RooK-Computer/RooK-Mk3/STLs/LegoInspiredCase_by_Konnexus_Mk1/CartridgeMk2-STLs/CartridgeMk2-TopPanel.stl

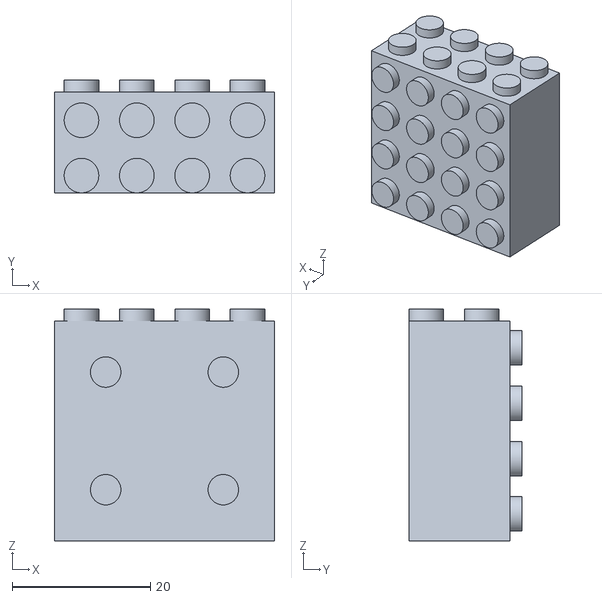
[picture p16: CAD file, 2025-09-18]
STLs/LegoInspiredCase_by_Konnexus_Mk1/CartridgeMk2-STLs/CartridgeMk2-TopPanel.stl
31.8 x 16.3 x 33.5
