RooK-Computer/RooK-Mk3/STLs/LegoInspiredCase_by_Konnexus_Mk1/CartridgeMk2-STLs/CartridgeMk2-FrontSide.stl

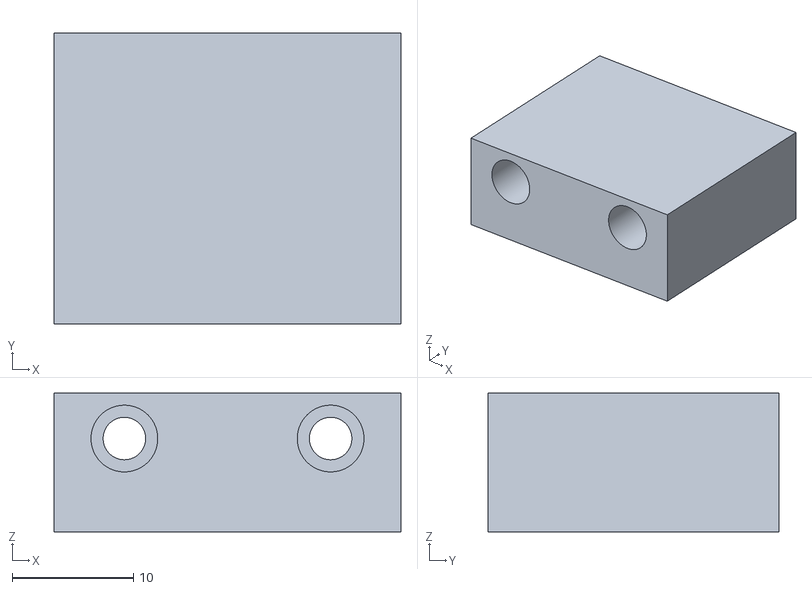
[picture p17: CAD file, 2025-09-12]
STLs/LegoInspiredCase_by_Konnexus_Mk1/CartridgeMk2-STLs/CartridgeMk2-FrontSide.stl
28.6 x 24.0 x 11.5
