RooK-Computer/RooK-Mk3/STLs/LegoInspiredCase_by_Konnexus_Mk1/Case-STLs/LegoCase_Konnexus_Mk1-Quit Button fat Border.stl

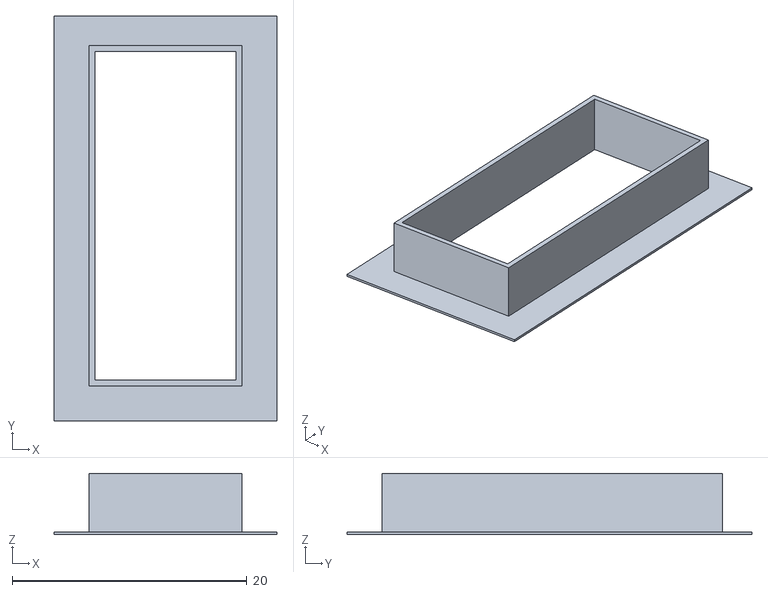
[picture p18: CAD file, 2025-09-19]
STLs/LegoInspiredCase_by_Konnexus_Mk1/Case-STLs/LegoCase_Konnexus_Mk1-Quit Button fat Border.stl
19.0 x 34.5 x 5.20
