RooK-Computer/RooK-Mk3/STLs/LegoInspiredCase_by_Konnexus_Mk1/CartridgeMk2-STLs/CartridgeMk2-Housing.stl

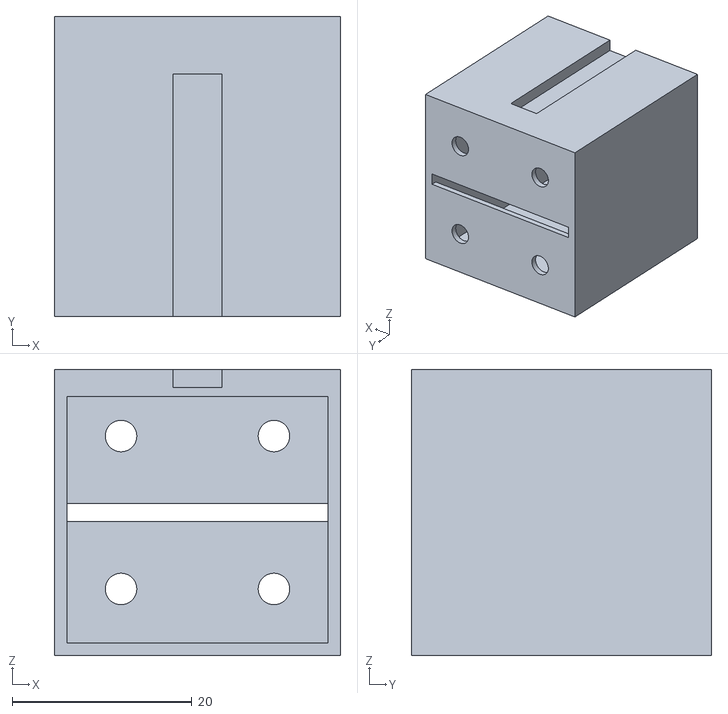
[picture p19: CAD file, 2025-09-12]
STLs/LegoInspiredCase_by_Konnexus_Mk1/CartridgeMk2-STLs/CartridgeMk2-Housing.stl
31.8 x 33.4 x 31.8
