RooK-Computer/RooK-Mk3/STLs/LegoInspiredCase_by_Konnexus_Mk1/Case-STLs/LegoCase_Konnexus_Mk1-Quit Button fat revised.stl

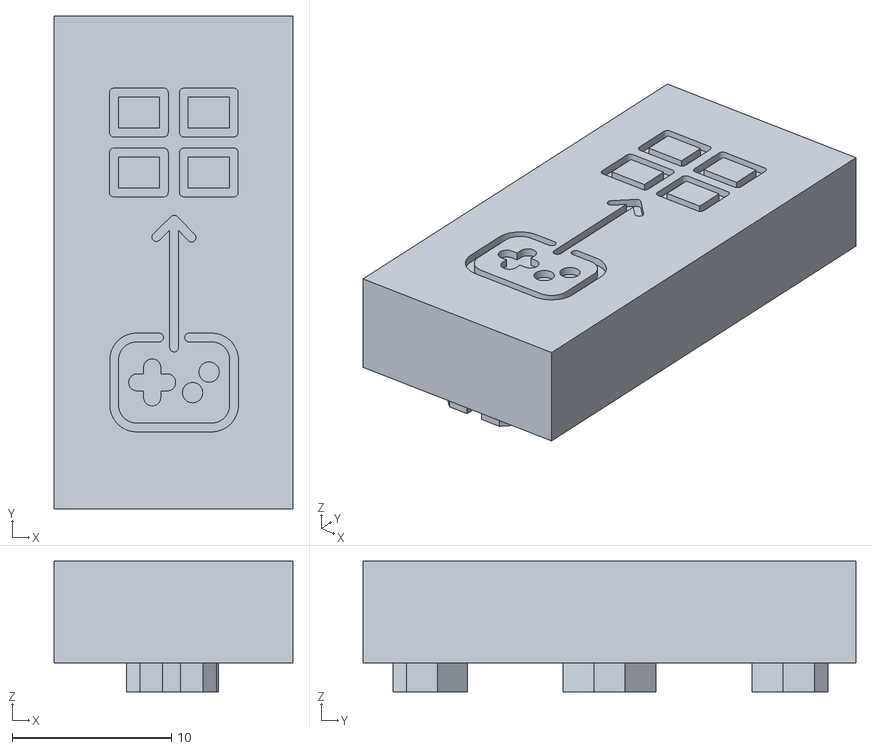
[picture p20: CAD file, 2025-09-19]
STLs/LegoInspiredCase_by_Konnexus_Mk1/Case-STLs/LegoCase_Konnexus_Mk1-Quit Button fat revised.stl
15.0 x 31.0 x 8.21
