RooK-Computer/RooK-Mk3/STLs/LegoInspiredCase_by_Konnexus_Mk1/Case-STLs/LegoCase_Konnexus_Mk1-Shutdown Button Print.stl

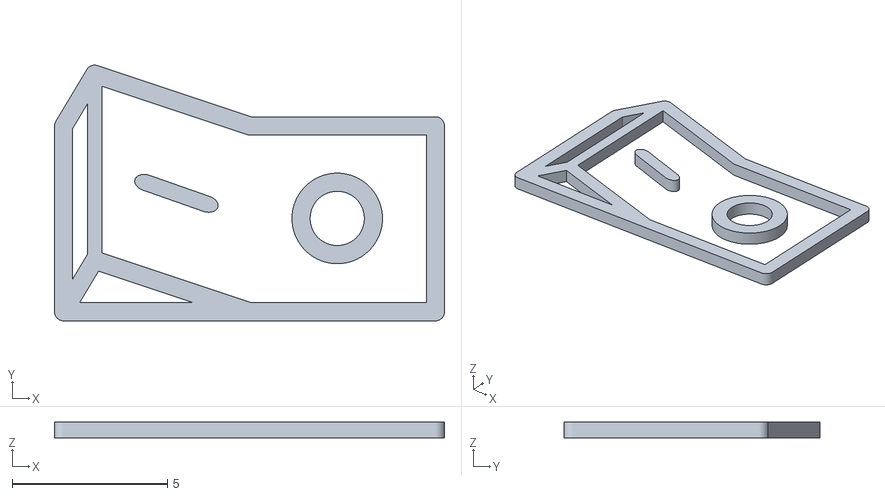
[picture p21: CAD file, 2025-09-12]
STLs/LegoInspiredCase_by_Konnexus_Mk1/Case-STLs/LegoCase_Konnexus_Mk1-Shutdown Button Print.stl
12.6 x 8.24 x 0.5
