RooK-Computer/RooK-Mk3/STLs/LegoInspiredCase_by_Konnexus_Mk1/Case-STLs/LegoCase_Konnexus_Mk1-CaseBase.stl

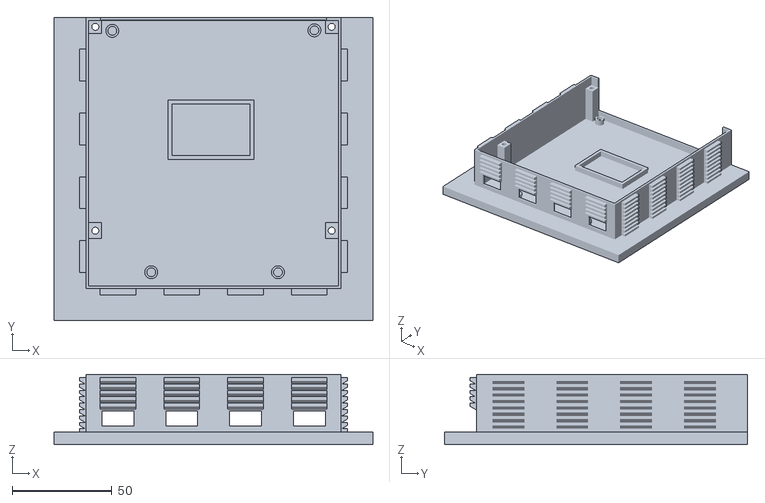
[picture p22: CAD file, 2025-09-12]
STLs/LegoInspiredCase_by_Konnexus_Mk1/Case-STLs/LegoCase_Konnexus_Mk1-CaseBase.stl
159.8 x 151.8 x 35.2
