RooK-Computer/RooK-Mk3/STLs/LegoInspiredCase_by_Konnexus_Mk1/Case-STLs/LegoCase_Konnexus_Mk1-cover embossed.stl

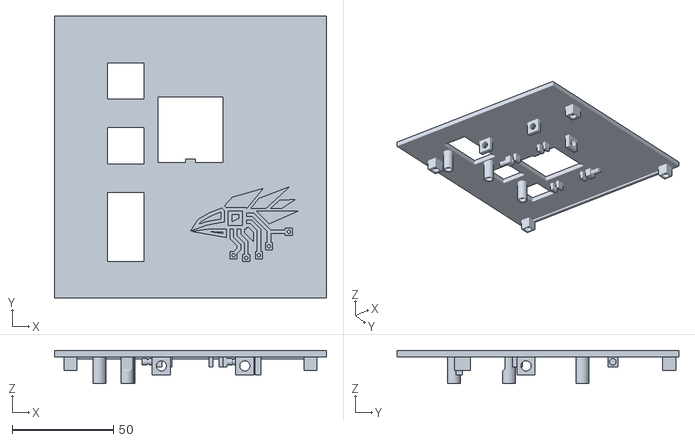
[picture p23: CAD file, 2025-09-12]
STLs/LegoInspiredCase_by_Konnexus_Mk1/Case-STLs/LegoCase_Konnexus_Mk1-cover embossed.stl
134.2 x 139.0 x 16.5
