RooK-Computer/RooK-Mk3/STLs/LegoInspiredCase_by_Konnexus_Mk1/Case-STLs/LegoCase_Konnexus_Mk1-KeySwitchSolderingHolder.stl

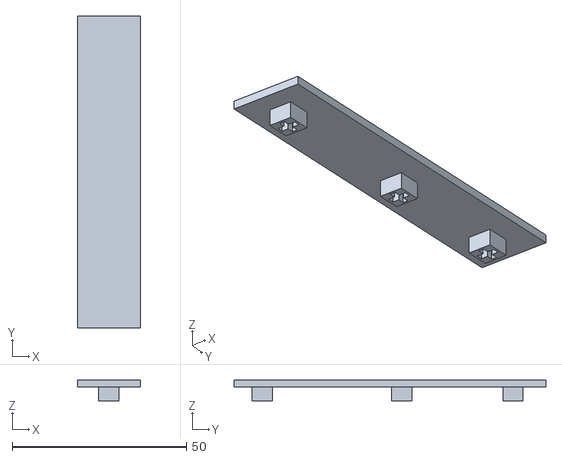
[picture p24: CAD file, 2025-09-12]
STLs/LegoInspiredCase_by_Konnexus_Mk1/Case-STLs/LegoCase_Konnexus_Mk1-KeySwitchSolderingHolder.stl
18.1 x 89.6 x 6.00
