RooK-Computer/RooK-Mk3/STLs/LegoInspiredCase_by_Konnexus_Mk1/Case-STLs/LegoCase_Konnexus_Mk1-Reset Button fat print.stl

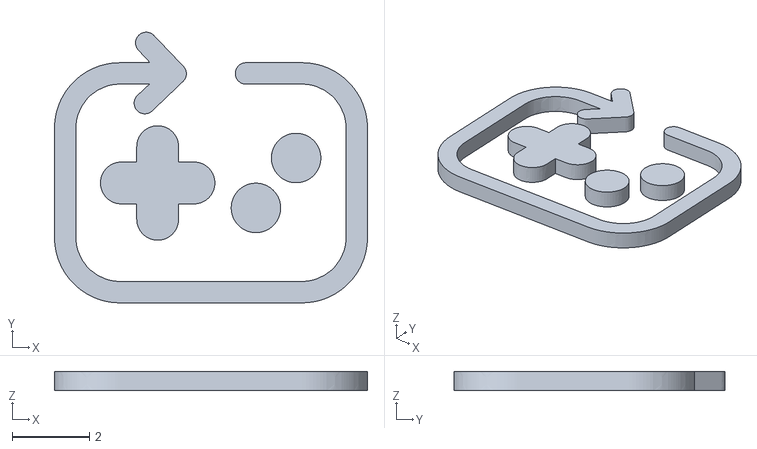
[picture p25: CAD file, 2025-09-12]
STLs/LegoInspiredCase_by_Konnexus_Mk1/Case-STLs/LegoCase_Konnexus_Mk1-Reset Button fat print.stl
8.09 x 7.00 x 0.5
