RooK-Computer/RooK-Mk3/PCBs/CartridgeReader/CartridgeMk3ReaderMk6/CartridgeMk3ReaderMk6.pdf

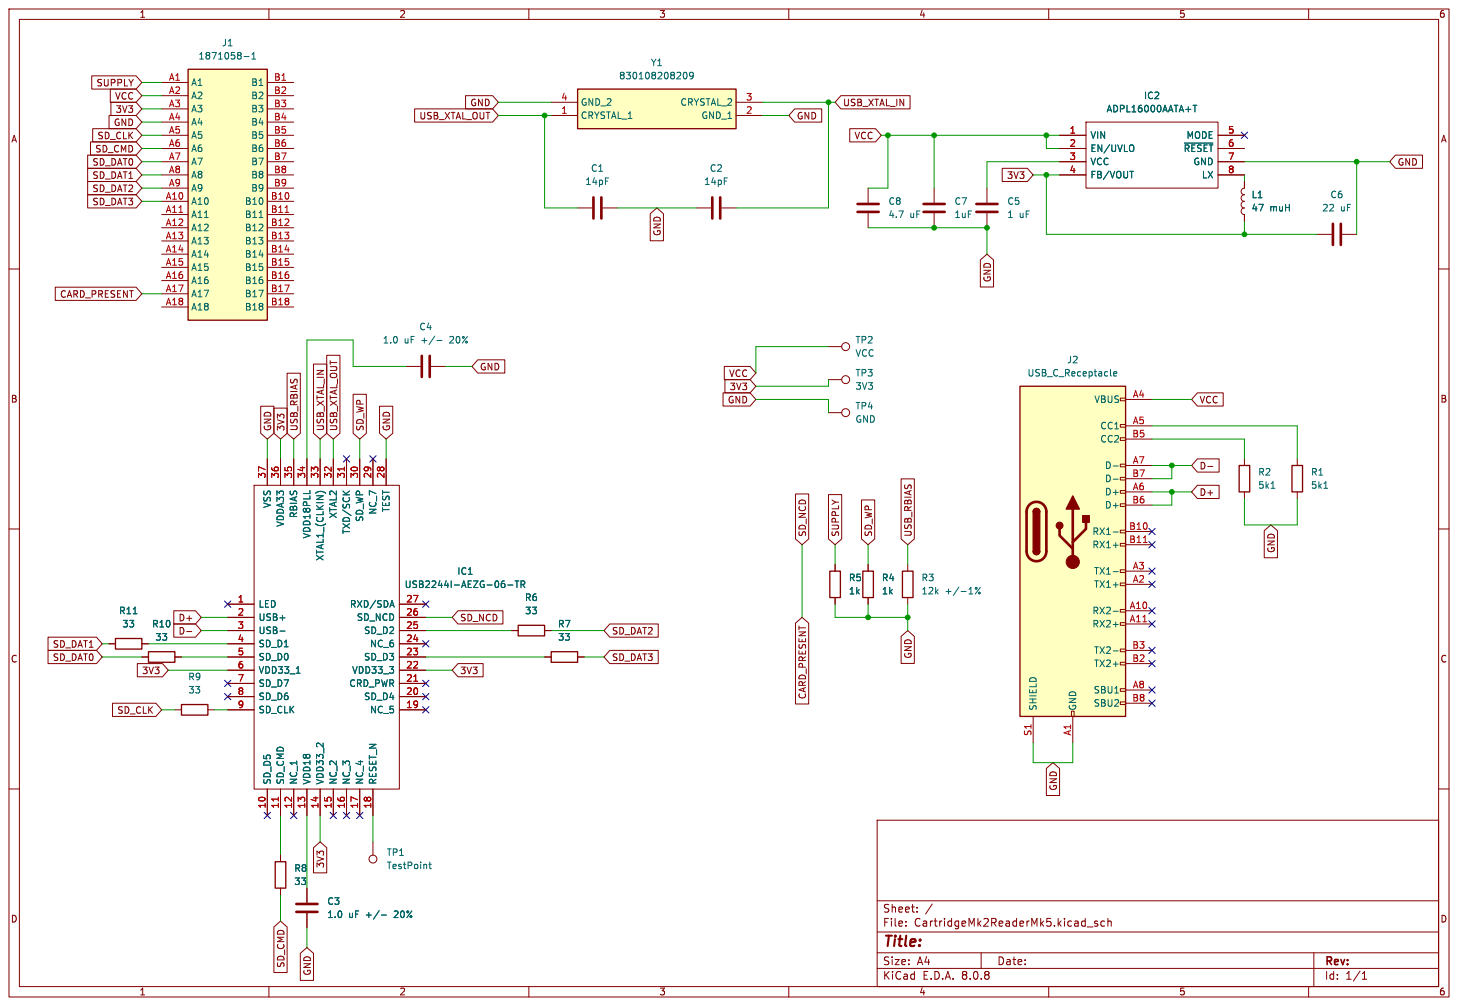
[picture p33: page 1]

Id: 1/1 Title: File: CartridgeMk2ReaderMk5.kicad_sch Sheet: /R3
