RooK-Computer/RooK-Mk3/PCBs/CM4-Files/CM4IO-KiCAD/CM4IOv5.kicad_sch

## KiCad design PCBs/CM4-Files/CM4IO-KiCAD/CM4IOv5.kicad_sch (2025-09-12)

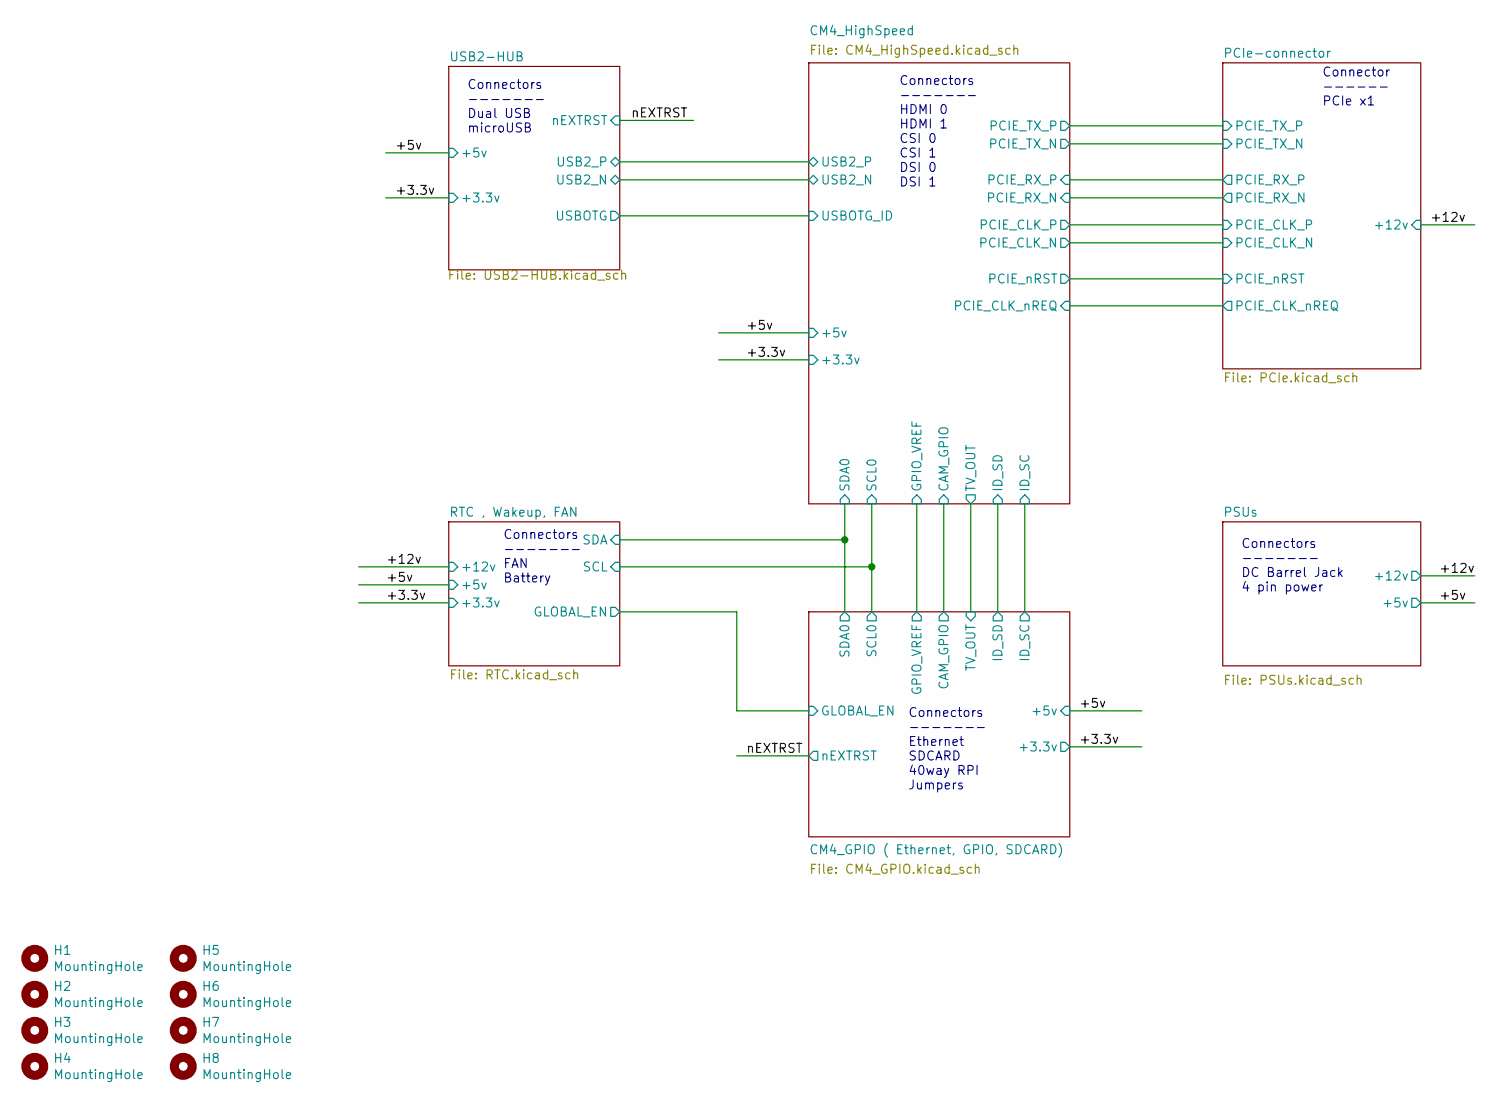
[picture p46: schematic CM4IOv5.kicad_sch]

Parts:
H1, H2, H3, H4, H5, H6, H7, H8: MountingHole; MountingHole_2.7mm_M2.5; Part Description M2.5 mounting hole

Notes on the sheet:
Connectors ------- FAN Battery
Connector ------ PCIe x1
Connectors ------- DC Barrel Jack 4 pin power
Connectors ------- Dual USB microUSB
Connectors ------- Ethernet SDCARD 40way RPI Jumpers
Connectors ------- HDMI 0 HDMI 1 CSI 0 CSI 1 DSI 0 DSI 1
