RooK-Computer/RooK-Mk3/PCBs/CM4-Files/CM4IO-KiCAD/CM4_GPIO.kicad_sch

## KiCad design PCBs/CM4-Files/CM4IO-KiCAD/CM4_GPIO.kicad_sch (2025-09-12)

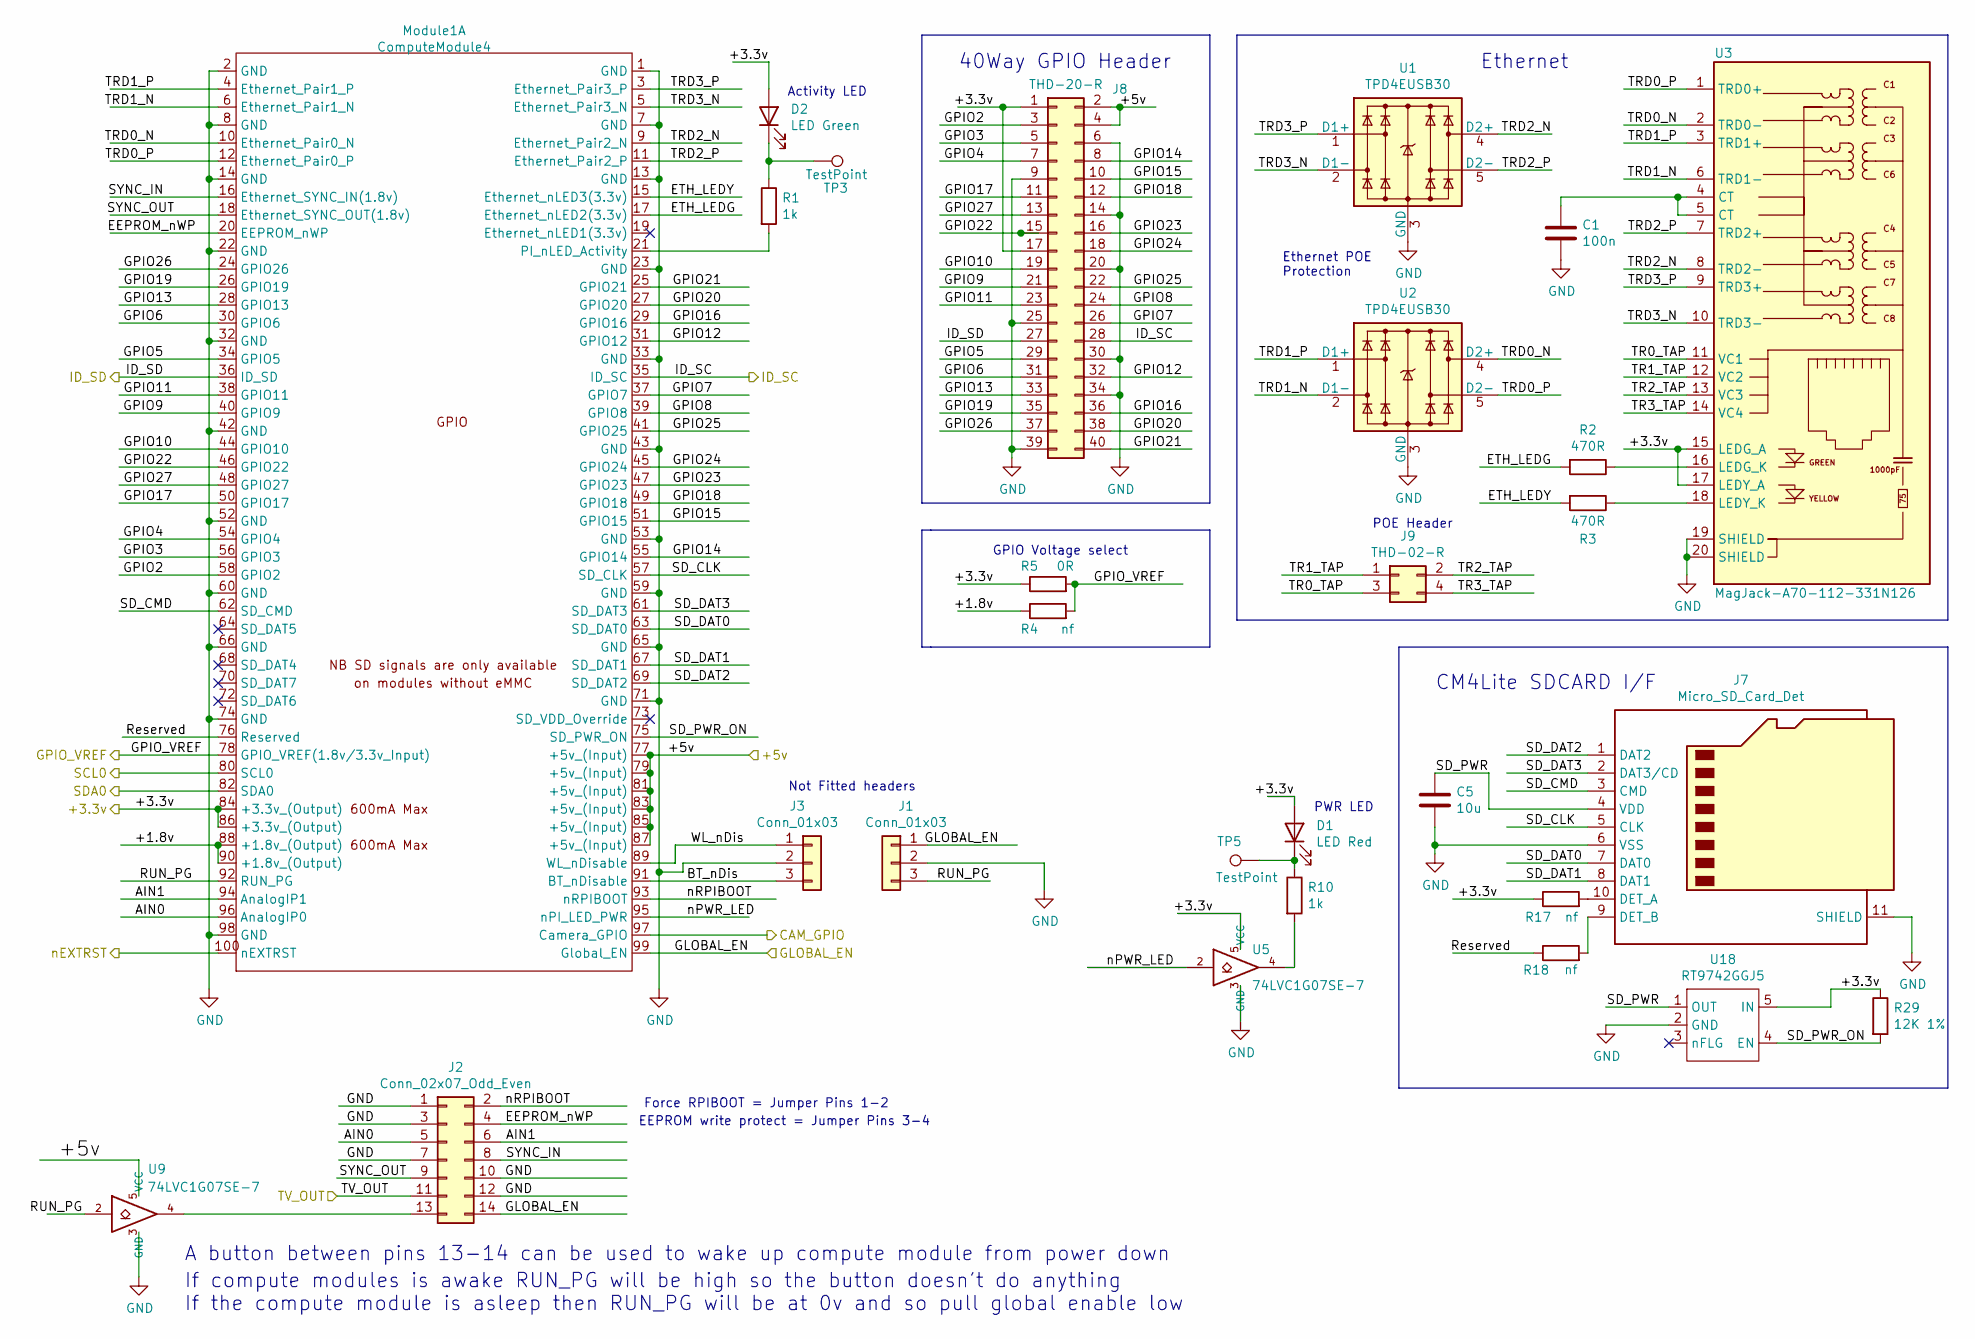
[picture p47: schematic CM4_GPIO.kicad_sch]

Parts:
C1: 100n; C_0402_1005Metric; Part Description 0.1uF 10% 16V Ceramic Capacitor X7R 040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
C5: 10u; C_0805_2012Metric; Part Description 10uF 10% 10V Ceramic Capacitor X7R 0805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
D1: LED Red; LED_0603_1608Metric; Part Description Red 620nm LED Indication - Discrete 2.2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
D2: LED Green; LED_0603_1608Metric; Part Description Green 572nm LED Indication - Discrete 2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
J1, J3: Conn_01x03; PinHeader_1x03_P2.54mm_Vertical; Part Description 3pin 0.1" connector
J2: Conn_02x07_Odd_Even; PinHeader_2x07_P2.54mm_Vertical; Part Description PinHeader_2x07_P2.54mm_Vertical
J7: Micro_SD_Card_Det; SDCARD_MOLEX_503398-1892; Part Description 9 (8 + 1) Position Card Connector micro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
J8: THD-20-R; PinHeader_2x20_P2.54mm_Vertical; Part Description PinHeader_2x20_P2.54mm_Vertical
J9: THD-02-R; PinHeader_2x02_P2.54mm_Vertical; Part Description PinHeader_2x02_P2.54mm_Vertical
Module1: ComputeModule4; Raspberry-Pi-4-Compute-Module; Part Description 100 Position Connector Receptacle, Cent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
R1, R10: 1k; R_0402_1005Metric; Part Description Resistor 1K M1005 1% 63mW
R2, R3: 470R; R_0402_1005Metric; Part Description Resistor 470R M1005 1% 63mW
R4: nf; R_0805_2012Metric_Pad1.15x1.40mm_HandSolder
R5: 0R; R_0805_2012Metric_Pad1.15x1.40mm_HandSolder; Part Description Resistor 0R M2012 5%
R17, R18: nf; R_0402_1005Metric; Part Description Resistor 1K M1005 1% 63mW
R29: 12K 1%; R_0402_1005Metric; Part Description Resistor 12K M1005 1% 63mW
TP3, TP5: TestPoint; TestPoint_Pad_2.0x2.0mm
U1, U2: TPD4EUSB30; USON-10_2.5x1.0mm_P0.5mm; Part Description Quad TVS diode for high speed signals (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
U3: MagJack-A70-112-331N126; TRJG0926HENL; Part Description Gigabit Ethernet Magjack
U5, U9: 74LVC1G07SE-7; SOT-353_SC-70-5; Part Description Buffer, Non-Inverting 1 Element 1 Bit p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
U18: RT9742GGJ5; SOT-23-5; Part Description Power Switch/Driver 1:1 N-Channel 1A TS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

Connections:
+1.8v: Module1.88 (+1.8v_(Output)), Module1.90 (+1.8v_(Output)), R4.1
+3.3v: D1.2 (A), D2.2 (A), J8.1, J8.17, Module1.84 (+3.3v_(Output)), Module1.86 (+3.3v_(Output)), R5.1, R17.1, R29.1, U3.15 (LEDG_A), U3.17 (LEDY_A), U5.5 (VCC), U18.5 (IN)
+5v: J8.2, J8.4, Module1.77 (+5v_(Input)), Module1.79 (+5v_(Input)), Module1.81 (+5v_(Input)), Module1.83 (+5v_(Input)), Module1.85 (+5v_(Input)), Module1.87 (+5v_(Input)), U9.5 (VCC)
AIN0: J2.5, Module1.96 (AnalogIP0)
AIN1: J2.6, Module1.94 (AnalogIP1)
BT_nDis: J3.3, Module1.91 (BT_nDisable)
CAM_GPIO: Module1.97 (Camera_GPIO)
EEPROM_nWP: J2.4, Module1.20 (EEPROM_nWP)
ETH_LEDG: Module1.17 (Ethernet_nLED2(3.3v)), R2.2
ETH_LEDY: Module1.15 (Ethernet_nLED3(3.3v)), R3.2
GLOBAL_EN: J1.1, J2.14, Module1.99 (Global_EN)
GND: C1.2, C5.2, J1.2, J2.1, J2.3, J2.7, J2.10, J2.12, J3.2, J7.6 (VSS), J7.11 (SHIELD), J8.6, J8.9, J8.14, J8.20, J8.25, J8.30, J8.34, J8.39, Module1.1 (GND), Module1.2 (GND), Module1.7 (GND), Module1.8 (GND), Module1.13 (GND), Module1.14 (GND), Module1.22 (GND), Module1.23 (GND), Module1.32 (GND), Module1.33 (GND), Module1.42 (GND), Module1.43 (GND), Module1.52 (GND), Module1.53 (GND), Module1.59 (GND), Module1.60 (GND), Module1.65 (GND), Module1.66 (GND), Module1.71 (GND), Module1.74 (GND), Module1.98 (GND), U1.3 (GND), U1.8 (GND), U2.3 (GND), U2.8 (GND), U3.19 (SHIELD), U3.20 (SHIELD), U5.3 (GND), U9.3 (GND), U18.2 (GND)
GPIO2: J8.3, Module1.58 (GPIO2)
GPIO3: J8.5, Module1.56 (GPIO3)
GPIO4: J8.7, Module1.54 (GPIO4)
GPIO5: J8.29, Module1.34 (GPIO5)
GPIO6: J8.31, Module1.30 (GPIO6)
GPIO7: J8.26, Module1.37 (GPIO7)
GPIO8: J8.24, Module1.39 (GPIO8)
GPIO9: J8.21, Module1.40 (GPIO9)
GPIO10: J8.19, Module1.44 (GPIO10)
GPIO11: J8.23, Module1.38 (GPIO11)
GPIO12: J8.32, Module1.31 (GPIO12)
GPIO13: J8.33, Module1.28 (GPIO13)
GPIO14: J8.8, Module1.55 (GPIO14)
GPIO15: J8.10, Module1.51 (GPIO15)
GPIO16: J8.36, Module1.29 (GPIO16)
GPIO17: J8.11, Module1.50 (GPIO17)
GPIO18: J8.12, Module1.49 (GPIO18)
GPIO19: J8.35, Module1.26 (GPIO19)
GPIO20: J8.38, Module1.27 (GPIO20)
GPIO21: J8.40, Module1.25 (GPIO21)
GPIO22: J8.15, Module1.46 (GPIO22)
GPIO23: J8.16, Module1.47 (GPIO23)
GPIO24: J8.18, Module1.45 (GPIO24)
GPIO25: J8.22, Module1.41 (GPIO25)
GPIO26: J8.37, Module1.24 (GPIO26)
GPIO27: J8.13, Module1.48 (GPIO27)
GPIO_VREF: Module1.78 (GPIO_VREF(1.8v/3.3v_Input)), R4.2, R5.2
ID_SC: J8.28, Module1.35 (ID_SC)
ID_SD: J8.27, Module1.36 (ID_SD)
unnamed: C1.1, U3.4 (CT), U3.5 (CT)
unnamed: D1.1 (K), R10.1, TP5.1
unnamed: D2.1 (K), R1.1, TP3.1
unnamed: J2.13, U9.4
unnamed: J7.9 (DET_B), R18.2
unnamed: J7.10 (DET_A), R17.2
unnamed: Module1.21 (PI_nLED_Activity), R1.2
unnamed: R2.1, U3.16 (LEDG_K)
unnamed: R3.1, U3.18 (LEDY_K)
unnamed: R10.2, U5.4
RUN_PG: J1.3, Module1.92 (RUN_PG), U9.2
Reserved: Module1.76 (Reserved), R18.1
SCL0: Module1.80 (SCL0)
SDA0: Module1.82 (SDA0)
SD_CLK: J7.5 (CLK), Module1.57 (SD_CLK)
SD_CMD: J7.3 (CMD), Module1.62 (SD_CMD)
SD_DAT0: J7.7 (DAT0), Module1.63 (SD_DAT0)
SD_DAT1: J7.8 (DAT1), Module1.67 (SD_DAT1)
SD_DAT2: J7.1 (DAT2), Module1.69 (SD_DAT2)
SD_DAT3: J7.2 (DAT3/CD), Module1.61 (SD_DAT3)
SD_PWR: C5.1, J7.4 (VDD), U18.1 (OUT)
SD_PWR_ON: Module1.75 (SD_PWR_ON), R29.2, U18.4 (EN)
SYNC_IN: J2.8, Module1.16 (Ethernet_SYNC_IN(1.8v))
SYNC_OUT: J2.9, Module1.18 (Ethernet_SYNC_OUT(1.8v))
TR0_TAP: J9.3, U3.11 (VC1)
TR1_TAP: J9.1, U3.12 (VC2)
TR2_TAP: J9.2, U3.13 (VC3)
TR3_TAP: J9.4, U3.14 (VC4)
TRD0_N: Module1.10 (Ethernet_Pair0_N), U2.4 (D2+), U2.7, U3.2 (TRD0-)
TRD0_P: Module1.12 (Ethernet_Pair0_P), U2.5 (D2-), U2.6, U3.1 (TRD0+)
TRD1_N: Module1.6 (Ethernet_Pair1_N), U2.2 (D1-), U2.9, U3.6 (TRD1-)
TRD1_P: Module1.4 (Ethernet_Pair1_P), U2.1 (D1+), U2.10, U3.3 (TRD1+)
TRD2_N: Module1.9 (Ethernet_Pair2_N), U1.4 (D2+), U1.7, U3.8 (TRD2-)
TRD2_P: Module1.11 (Ethernet_Pair2_P), U1.5 (D2-), U1.6, U3.7 (TRD2+)
TRD3_N: Module1.5 (Ethernet_Pair3_N), U1.2 (D1-), U1.9, U3.10 (TRD3-)
TRD3_P: Module1.3 (Ethernet_Pair3_P), U1.1 (D1+), U1.10, U3.9 (TRD3+)
TV_OUT: J2.11
WL_nDis: J3.1, Module1.89 (WL_nDisable)
nEXTRST: Module1.100 (nEXTRST)
nPWR_LED: Module1.95 (nPI_LED_PWR), U5.2
nRPIBOOT: J2.2, Module1.93 (nRPIBOOT)

Notes on the sheet:
PWR LED
Ethernet POE Protection
40Way GPIO Header
CM4Lite SDCARD I/F
GPIO Voltage select
Ethernet
Activity LED
EEPROM write protect = Jumper Pins 3-4
Not Fitted headers
A button between pins 13-14 can be used to wake up compute module from power down
If compute modules is awake RUN_PG will be high so the button doesn't do anything If the compute module is asleep then RUN_PG will be at 0v and so pull global enable low
Force RPIBOOT = Jumper Pins 1-2
POE Header
