RooK-Computer/RooK-Mk3/PCBs/CM4-Files/CM4IO-KiCAD/PCIe.kicad_sch

## KiCad design PCBs/CM4-Files/CM4IO-KiCAD/PCIe.kicad_sch (2025-09-12)

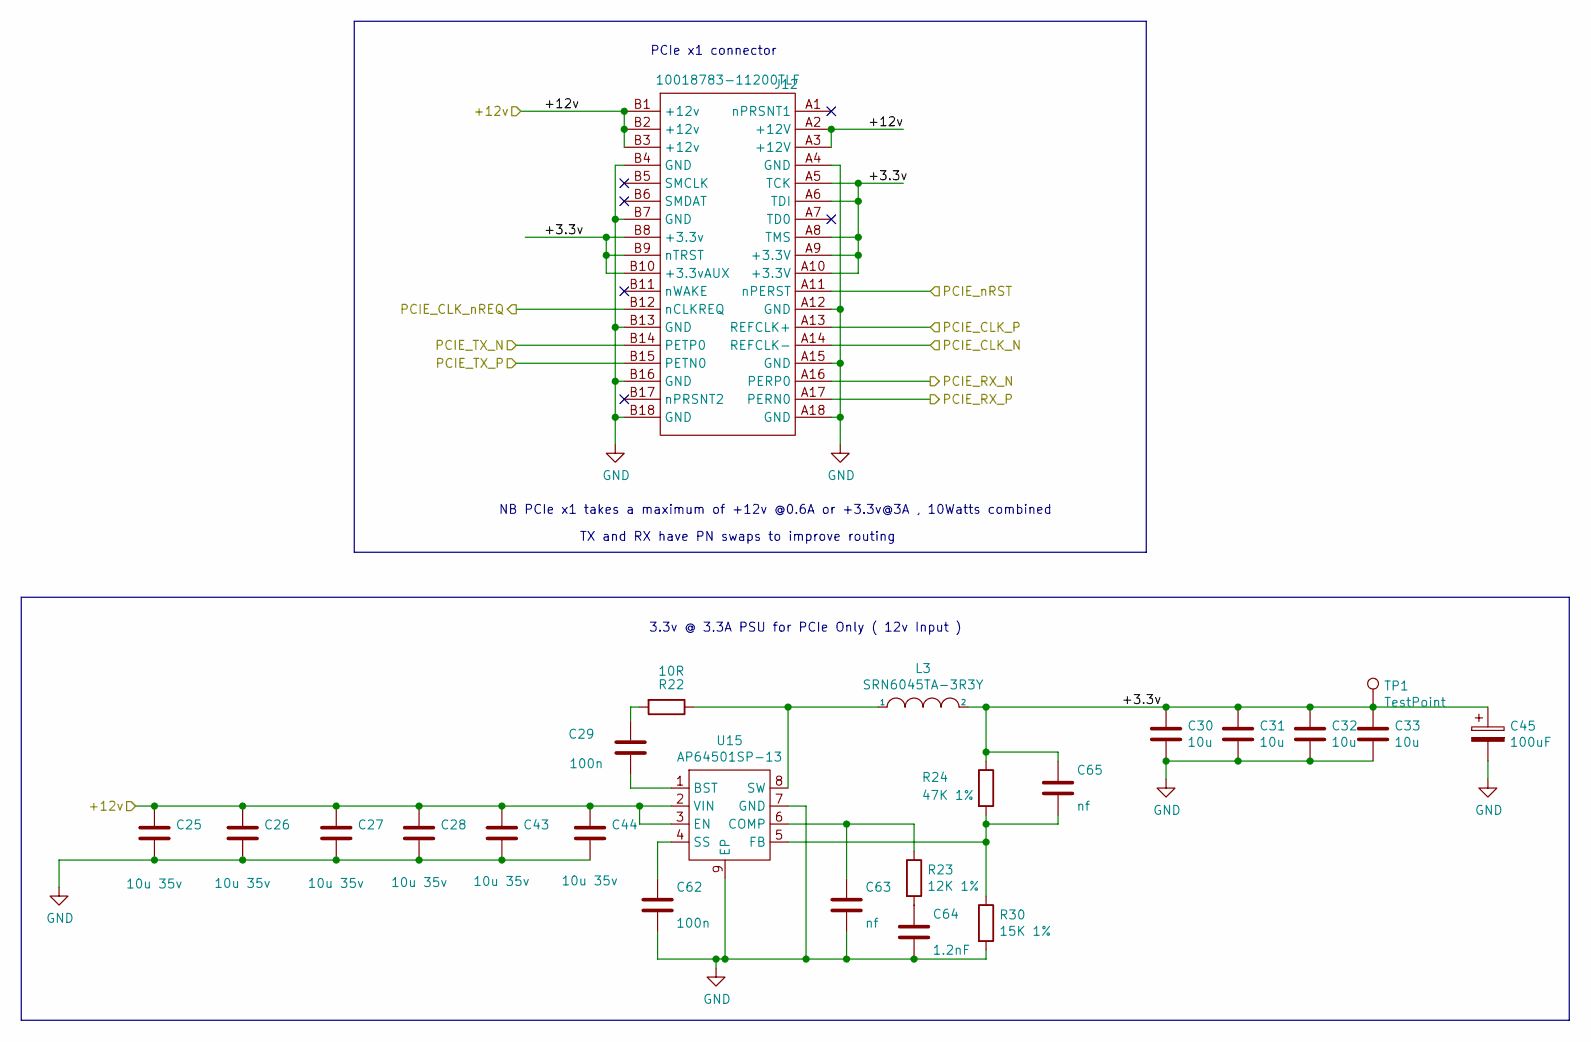
[picture p49: schematic PCIe.kicad_sch]

Parts:
C25, C26, C27, C28, C43, C44: 10u 35v; C_0805_2012Metric; Part Description 10uF 10% or 20% 35V Ceramic Capacitor X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
C29, C62: 100n; C_0402_1005Metric; Part Description 0.1uF 10% 16V Ceramic Capacitor X7R 040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
C30, C31, C32, C33: 10u; C_0805_2012Metric; Part Description 10uF 10% 10V Ceramic Capacitor X7R 0805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
C45: 100uF; CP_EIA-7343-31_Kemet-D; Part Description Capacitor, SP-Cap, 100u, 6.3V, 15mR ESR
C63: nf; C_0402_1005Metric
C64: 1.2nF; C_0402_1005Metric; Part Description 1200pF 10% 10V Ceramic Capacitor X5R 04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
C65: nf; C_0402_1005Metric; Part Description 27pF 5% 50V Ceramic Capacitor C0G, NP0 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
J12: 10018783-11200TLF; PCIex1-36; Part Description PCI Express/PCI Connectors PCIE THROUGH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
L3: SRN6045TA-3R3Y; L_Bourns_SRN6045TA; Part Description 3.3µH Semi-Shielded Wirewound Inductor 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
R22: 10R; R_0402_1005Metric; Part Description Resistor 10R M1005 1% 63mW
R23: 12K 1%; R_0402_1005Metric; Part Description Resistor 12K M1005 1% 63mW
R24: 47K 1%; R_0402_1005Metric; Part Description Resistor 47K M1005 1% 63mW
R30: 15K 1%; R_0402_1005Metric; Part Description Resistor 15K M1005 1% 63mW
TP1: TestPoint; TestPoint_Pad_2.0x2.0mm
U15: AP64501SP-13; SOIC-8-1EP_3.9x4.9mm_P1.27mm_EP2.95x4.9mm_Mask2.71x3.4mm_Th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; Part Description Buck Switching Regulator IC Positive Ad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

Connections:
+3.3v: C30.1, C31.1, C32.1, C33.1, C45.1, C65.1, J12.A5 (TCK), J12.A6 (TDI), J12.A8 (TMS), J12.A9 (+3.3V), J12.A10 (+3.3V), J12.B8 (+3.3v), J12.B9 (nTRST), J12.B10 (+3.3vAUX), L3.2, R24.1, TP1.1
+12v: C25.1, C26.1, C27.1, C28.1, C43.1, C44.1, J12.A2 (+12V), J12.A3 (+12V), J12.B1 (+12v), J12.B2 (+12v), J12.B3 (+12v), U15.2 (VIN), U15.3 (EN)
GND: C25.2, C26.2, C27.2, C28.2, C30.2, C31.2, C32.2, C33.2, C43.2, C44.2, C45.2, C62.2, C63.2, C64.2, J12.A4 (GND), J12.A12 (GND), J12.A15 (GND), J12.A18 (GND), J12.B4 (GND), J12.B7 (GND), J12.B13 (GND), J12.B16 (GND), J12.B18 (GND), R30.2, U15.7 (GND), U15.9 (EP)
unnamed: C29.1, R22.2
unnamed: C29.2, U15.1 (BST)
unnamed: C62.1, U15.4 (SS)
unnamed: C63.1, R23.1, U15.6 (COMP)
unnamed: C64.1, R23.2
unnamed: C65.2, R24.2, R30.1, U15.5 (FB)
unnamed: L3.1, R22.1, U15.8 (SW)
PCIE_CLK_N: J12.A14 (REFCLK-)
PCIE_CLK_P: J12.A13 (REFCLK+)
PCIE_CLK_nREQ: J12.B12 (nCLKREQ)
PCIE_RX_N: J12.A16 (PERP0)
PCIE_RX_P: J12.A17 (PERN0)
PCIE_TX_N: J12.B14 (PETP0)
PCIE_TX_P: J12.B15 (PETN0)
PCIE_nRST: J12.A11 (nPERST)

Notes on the sheet:
TX and RX have PN swaps to improve routing
PCIe x1 connector
3.3v @ 3.3A PSU for PCIe Only ( 12v Input )
NB PCIe x1 takes a maximum of +12v @0.6A or +3.3v@3A , 10Watts combined
